flyCouch/auroraLink/pics/CdSHolder_IMG_20260207_105626637.jpg

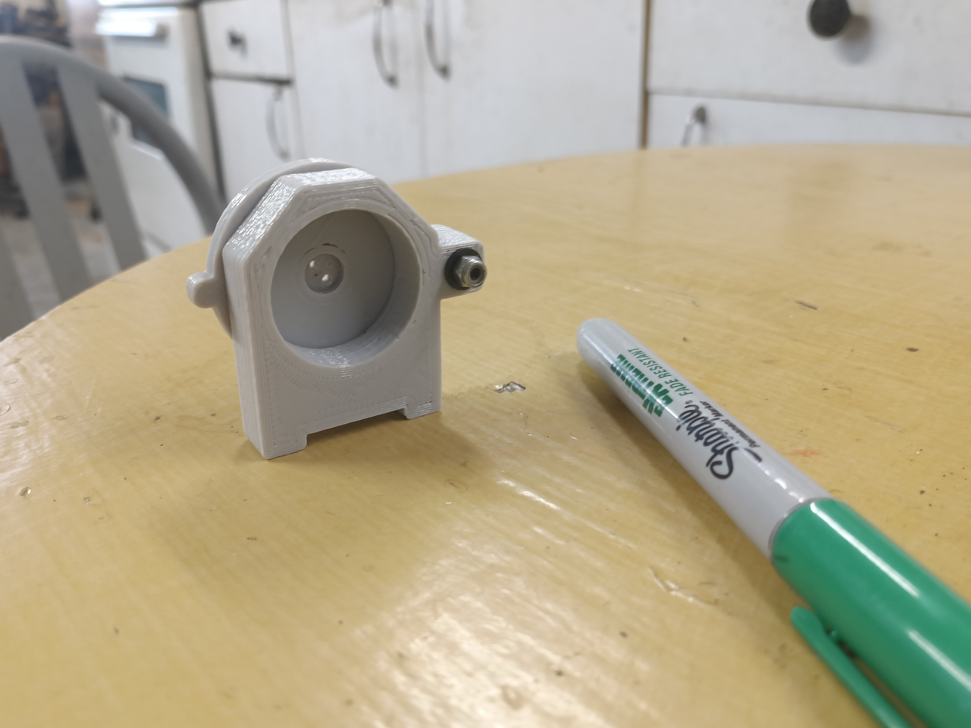
pics/CdSHolder_IMG_20260207_105626637.jpg
