flyCouch/auroraLink/pics/CdSHolder_IMG_20260207_105712110.jpg

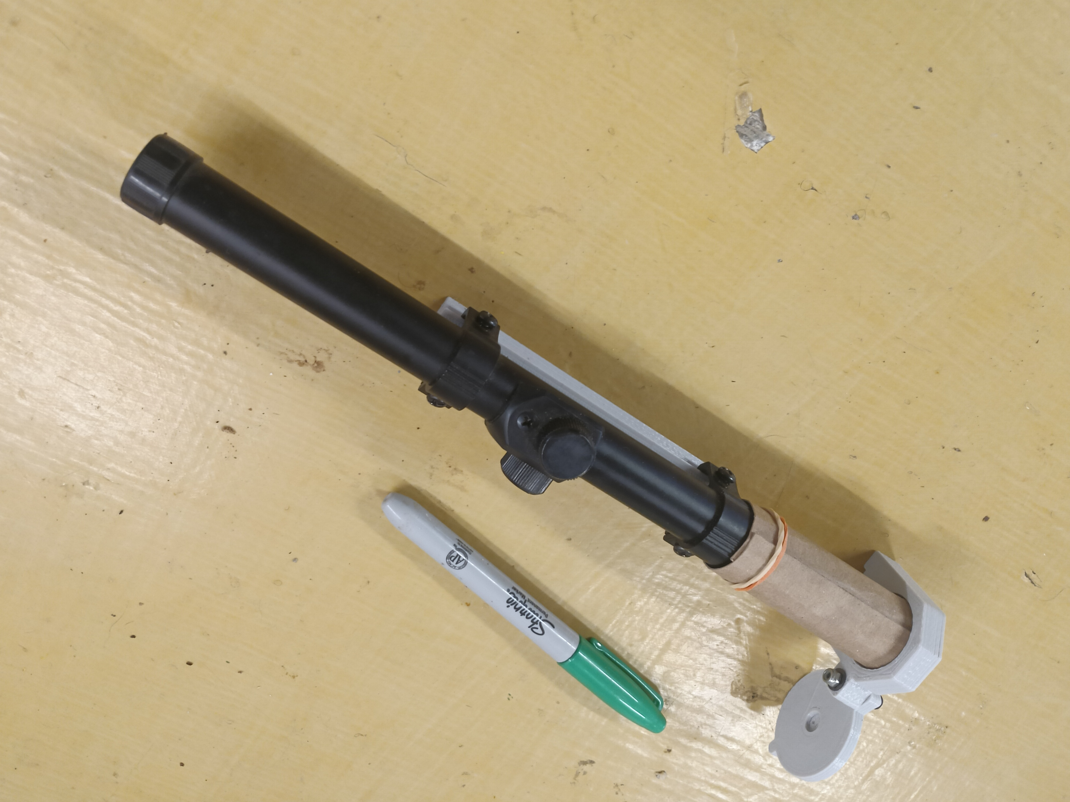
pics/CdSHolder_IMG_20260207_105712110.jpg
