flyCouch/auroraLink/pics/completeModule_IMG_20260208_100738802.jpg

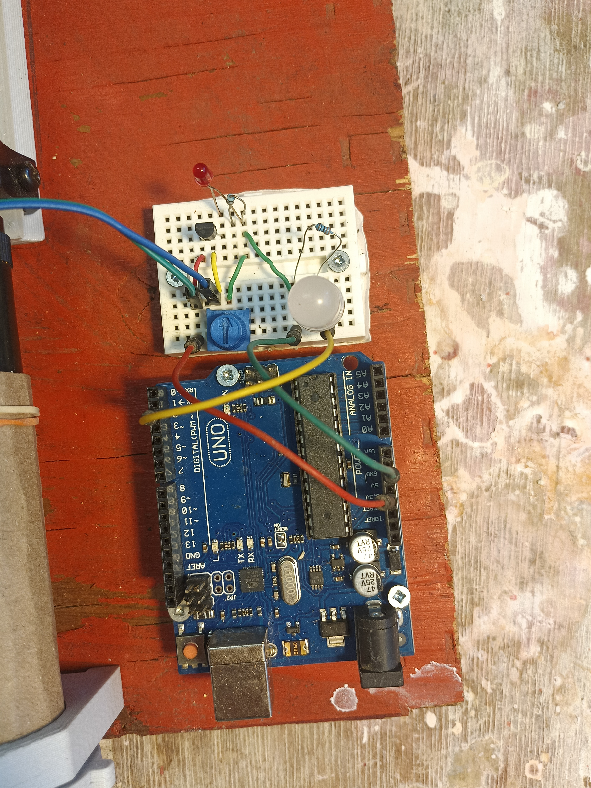
pics/completeModule_IMG_20260208_100738802.jpg
